srozum/film_camera_tester/assets/images/enclosure-1.jpg

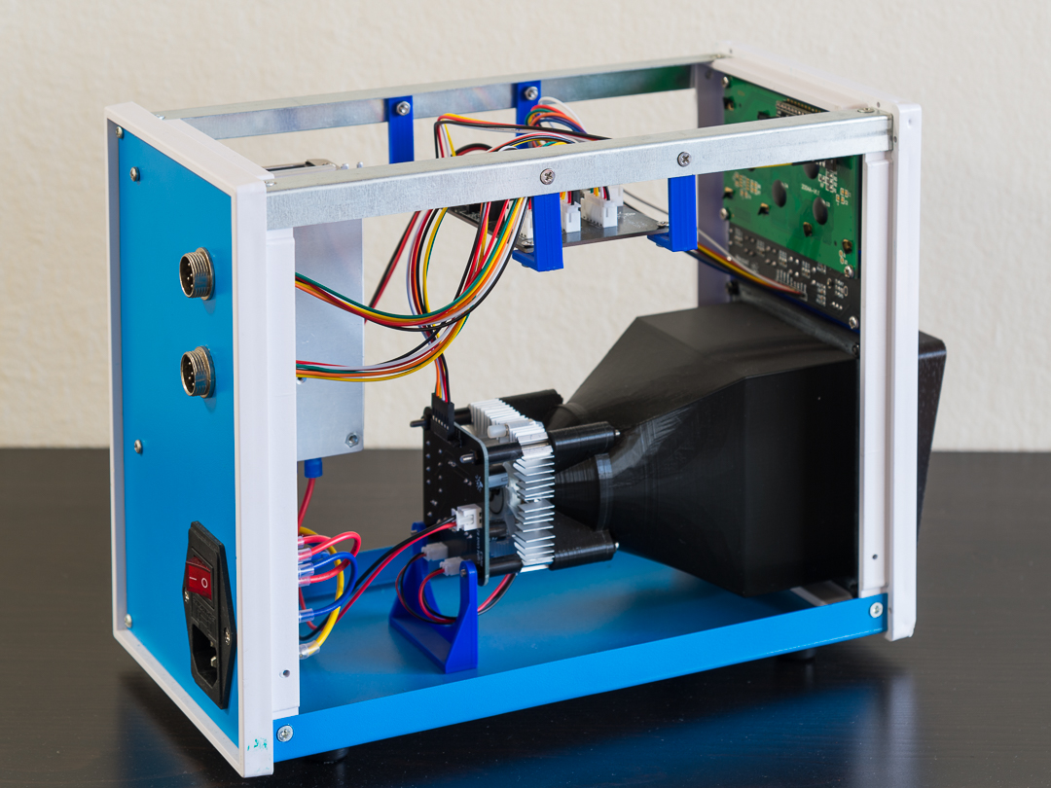
assets/images/enclosure-1.jpg
