srozum/film_camera_tester/assets/images/enclosure-2.jpg

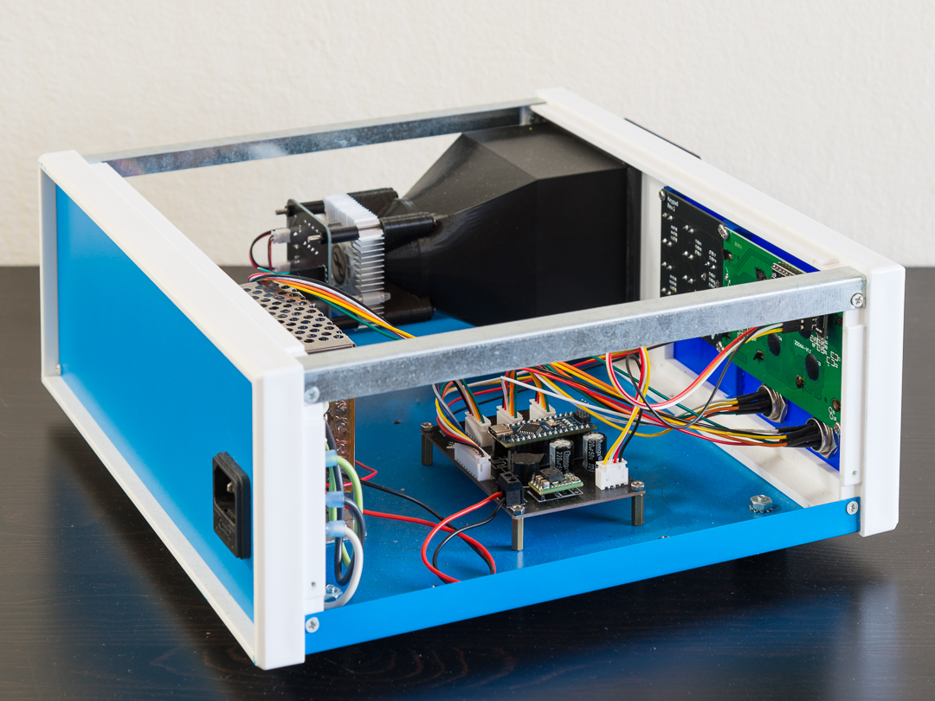
assets/images/enclosure-2.jpg
