srozum/film_camera_tester/assets/images/laser sensor module.jpeg

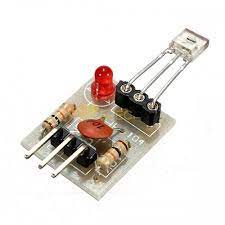
assets/images/laser sensor module.jpeg
