srozum/film_camera_tester/assets/images/light-unit-2-small-5.jpg

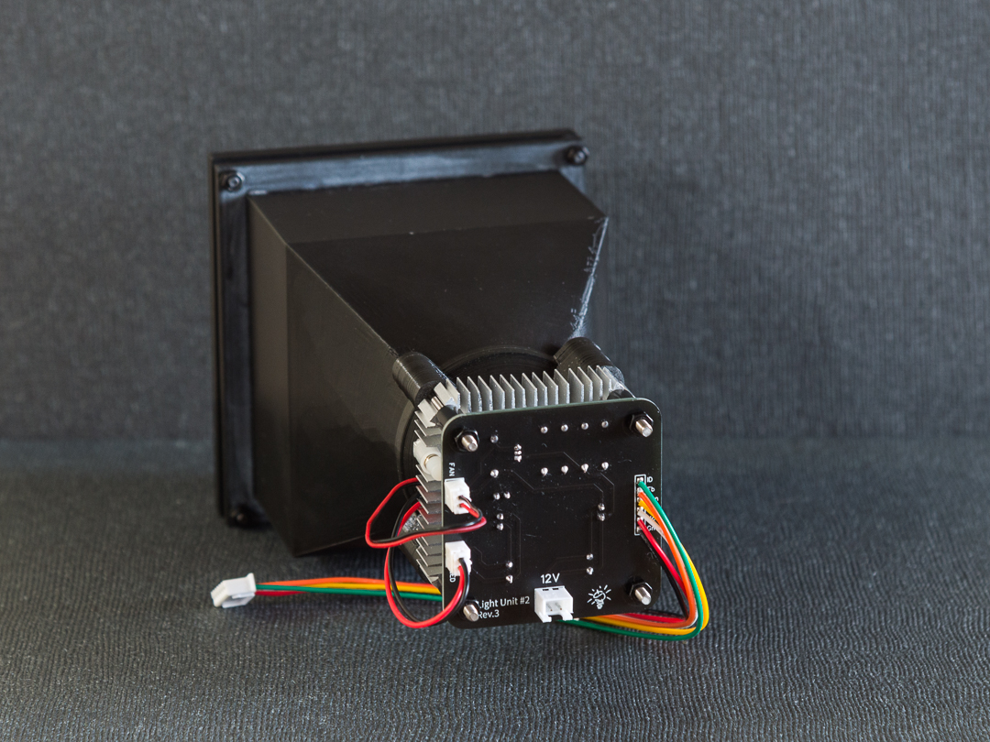
assets/images/light-unit-2-small-5.jpg
