srozum/film_camera_tester/assets/images/product-small-2.jpg

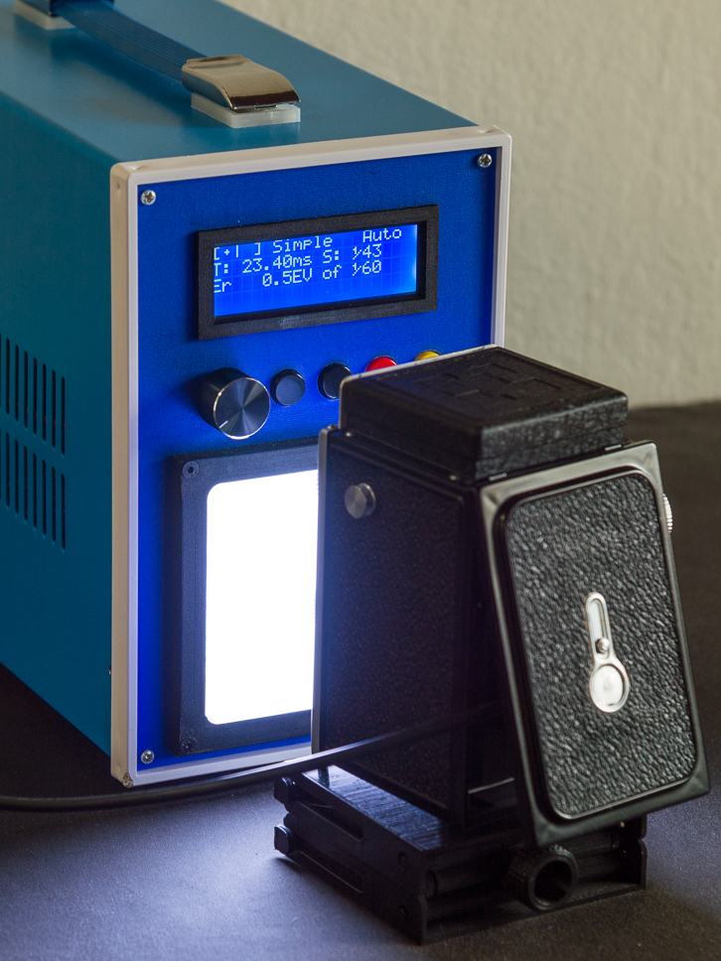
assets/images/product-small-2.jpg
