srozum/film_camera_tester/assets/images/product-small-3.jpg

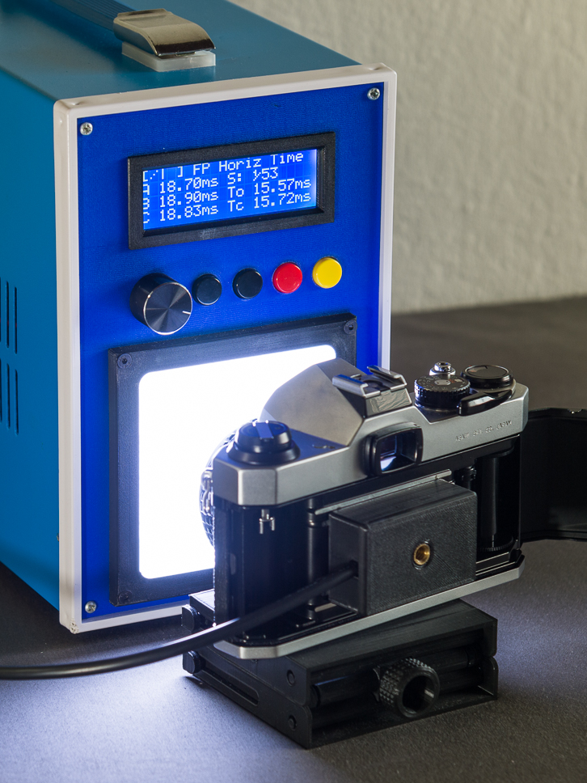
assets/images/product-small-3.jpg
