srozum/film_camera_tester/assets/images/product-small-4.jpg

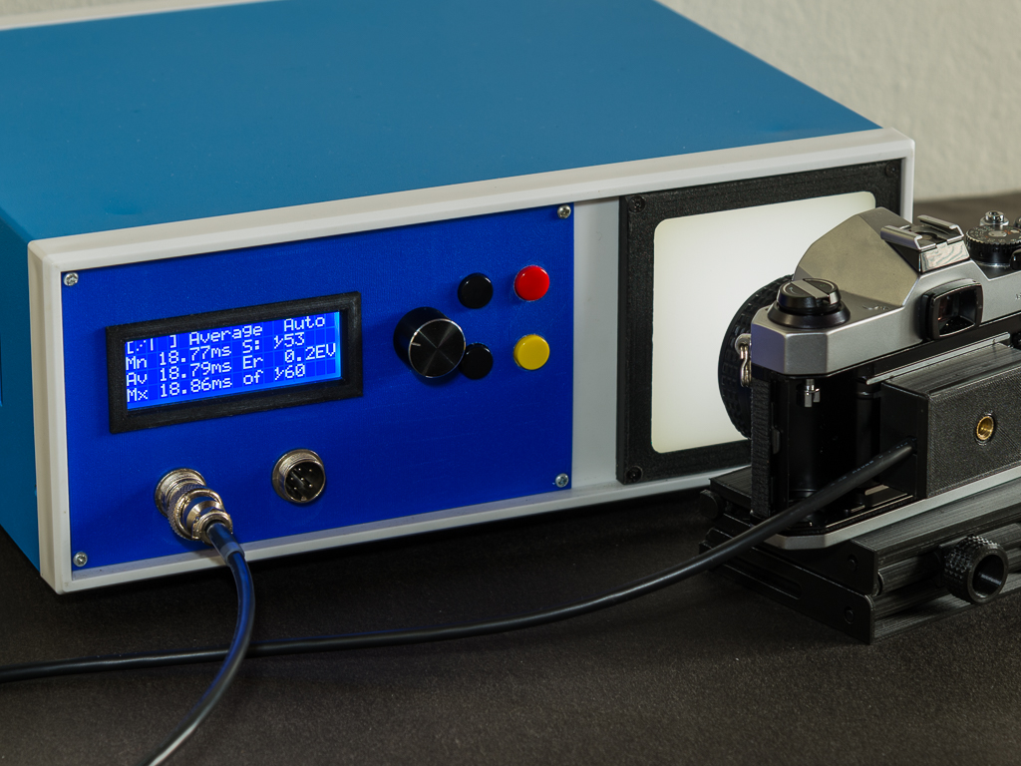
assets/images/product-small-4.jpg
