srozum/film_camera_tester/assets/schematics/keypad.png

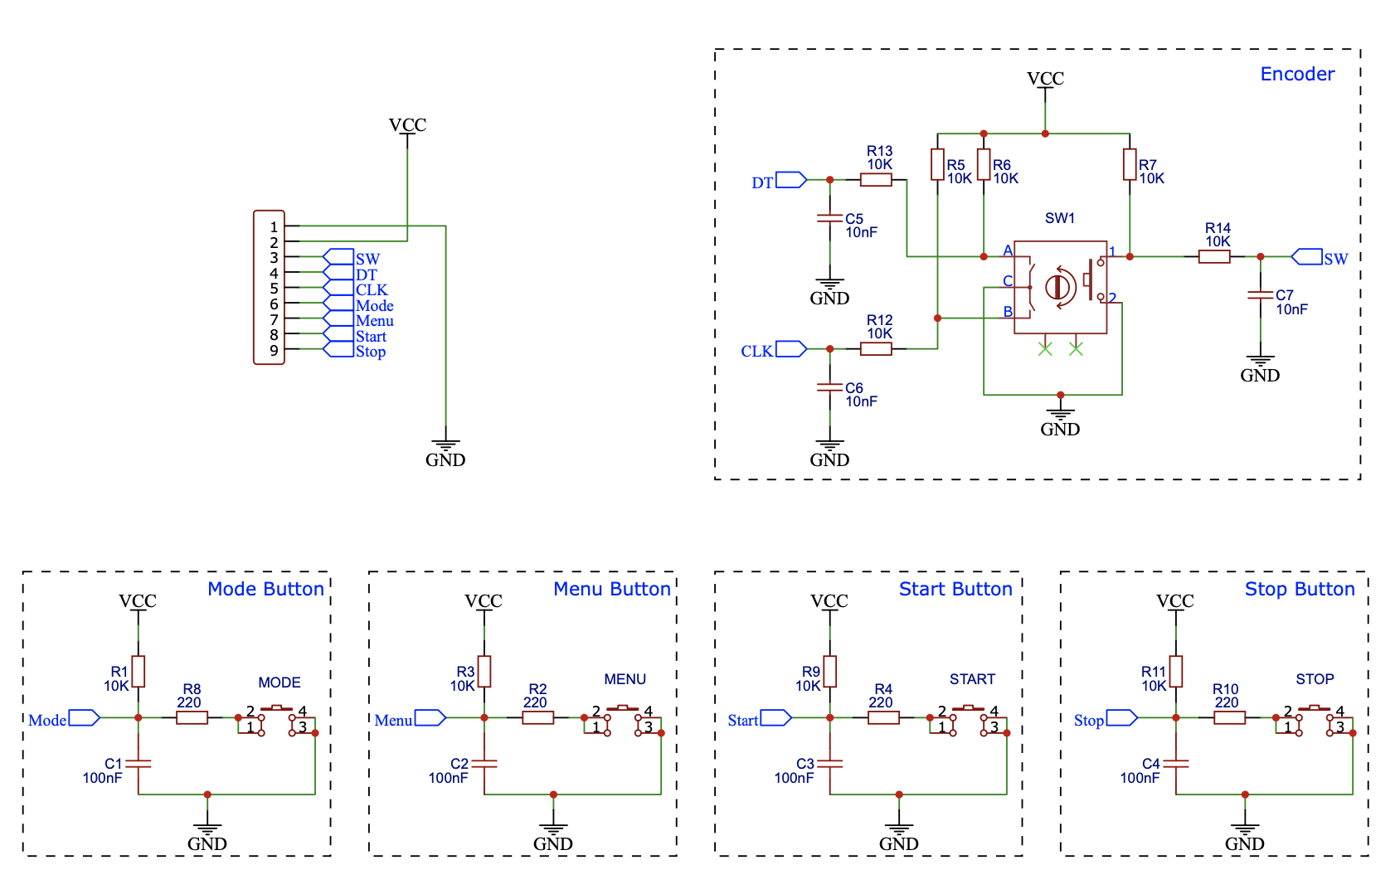
assets/schematics/keypad.png
