srozum/film_camera_tester/assets/schematics/light-unit-1.png

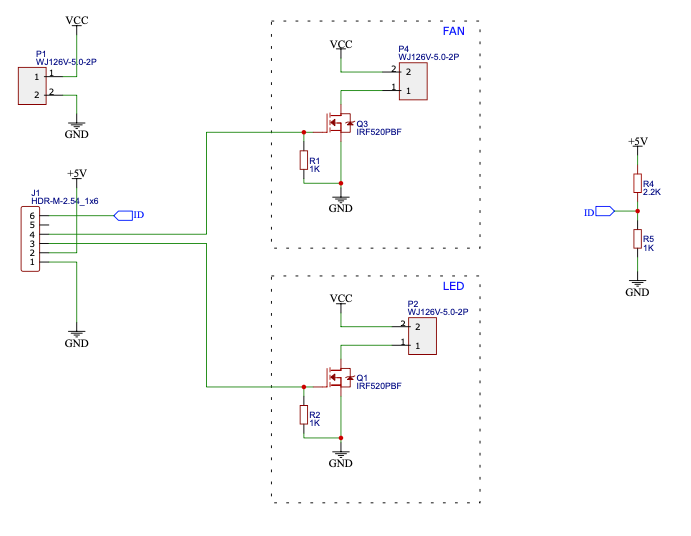
assets/schematics/light-unit-1.png
