srozum/film_camera_tester/assets/schematics/light-unit-2.png

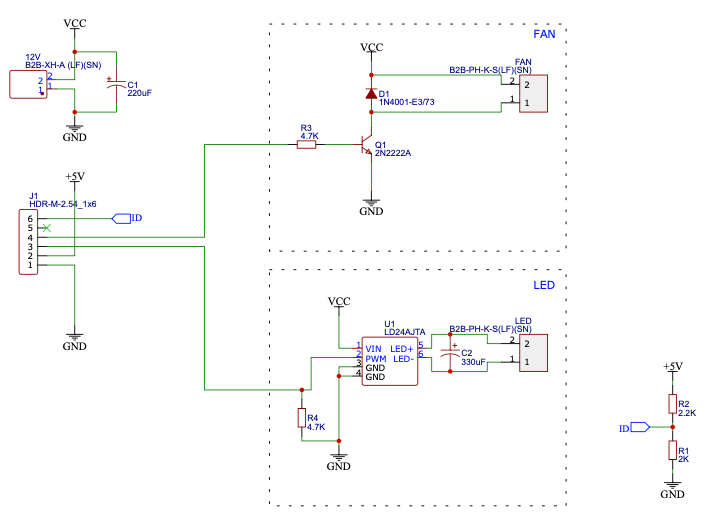
assets/schematics/light-unit-2.png
