srozum/film_camera_tester/assets/schematics/sensor3-v1.png

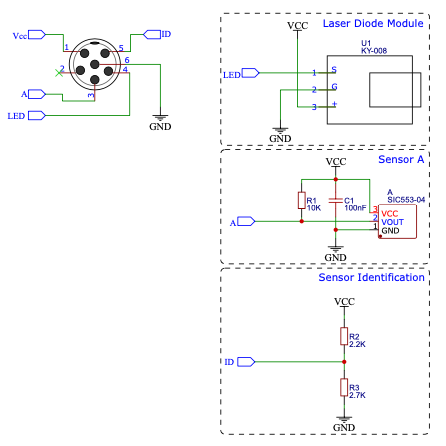
assets/schematics/sensor3-v1.png
