srozum/film_camera_tester/assets/schematics/shield-v2-rev-2.png

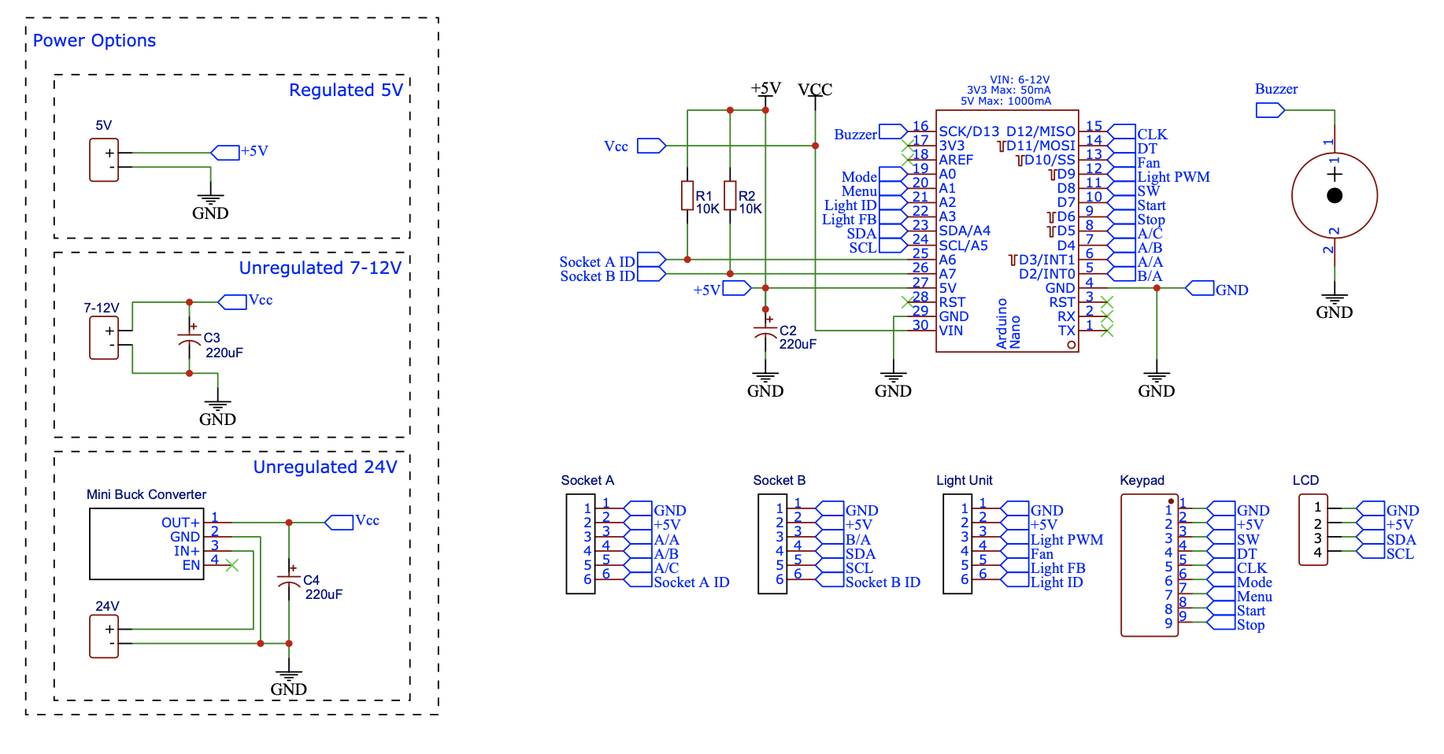
assets/schematics/shield-v2-rev-2.png
