srozum/film_camera_tester/assets/schematics/sockets.png

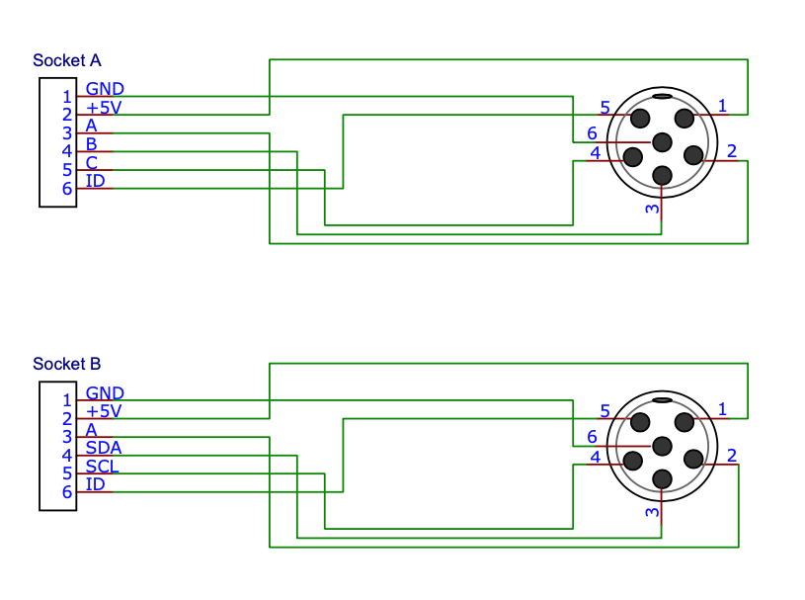
assets/schematics/sockets.png
