srozum/film_camera_tester/assets/screenshots/screen-19.png

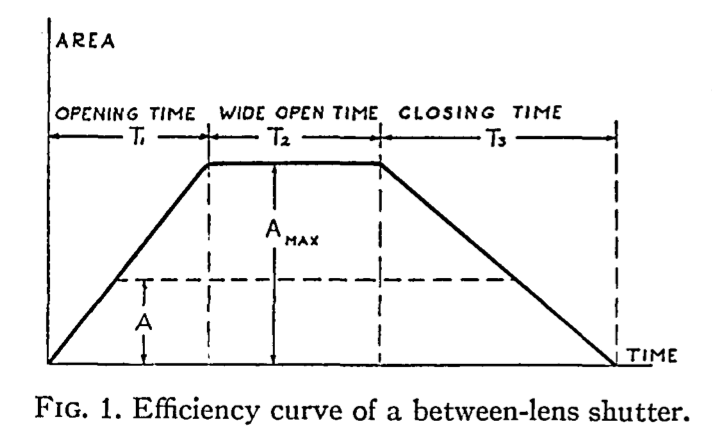
assets/screenshots/screen-19.png
