srozum/film_camera_tester/assets/stl/sensor-1/body.stl

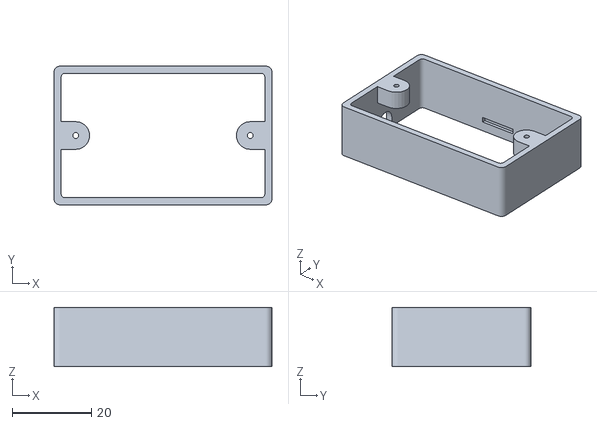
[picture p44: CAD file, 2022-08-05, an earlier design]
assets/stl/sensor-1/body.stl
55.0 x 35.0 x 15.0
