srozum/film_camera_tester/assets/stl/sensor-2/medium_format_adapter.stl

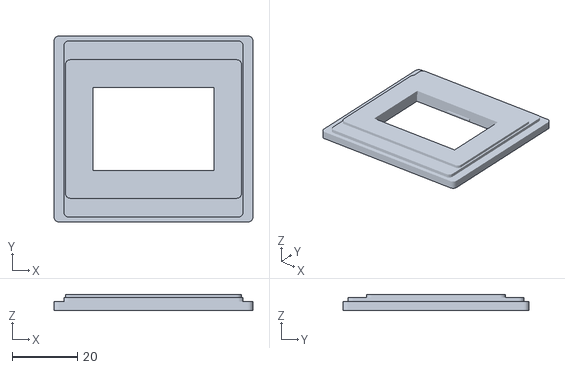
[picture p45: CAD file, 2022-08-05, an earlier design]
assets/stl/sensor-2/medium_format_adapter.stl
61.0 x 57.0 x 5.00
