srozum/film_camera_tester/assets/stl/sensor-1/face_plate.stl

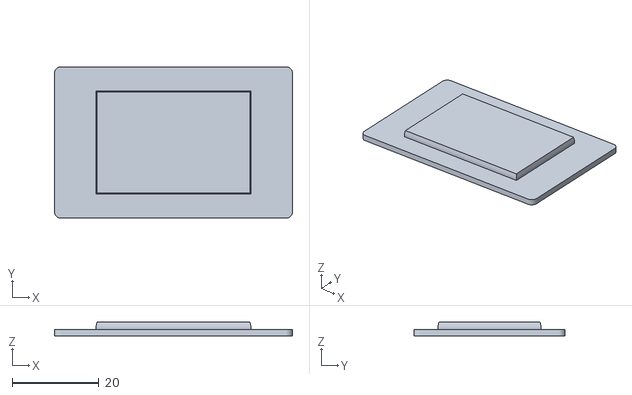
[picture p46: CAD file, 2022-08-05, an earlier design]
assets/stl/sensor-1/face_plate.stl
55.0 x 35.0 x 3.25
