srozum/film_camera_tester/assets/stl/sensor-2/body.stl

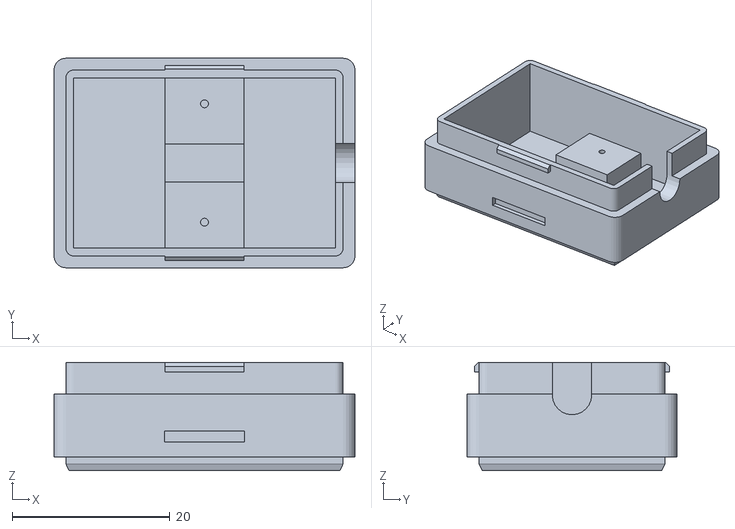
[picture p47: CAD file, 2022-08-05, an earlier design]
assets/stl/sensor-2/body.stl
38.2 x 26.6 x 13.8
